DjVul/Nixie-Clock-V1/Aesthetic/DSC_0027.JPG

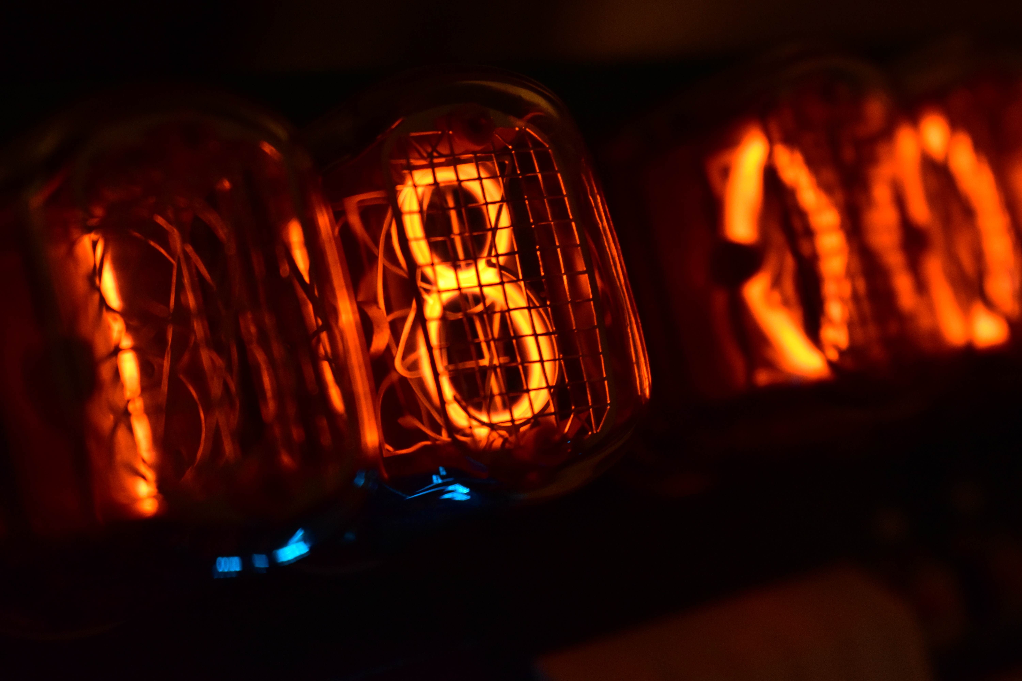
Aesthetic/DSC_0027.JPG
