DjVul/Nixie-Clock-V1/Aesthetic/DSC_0036.JPG

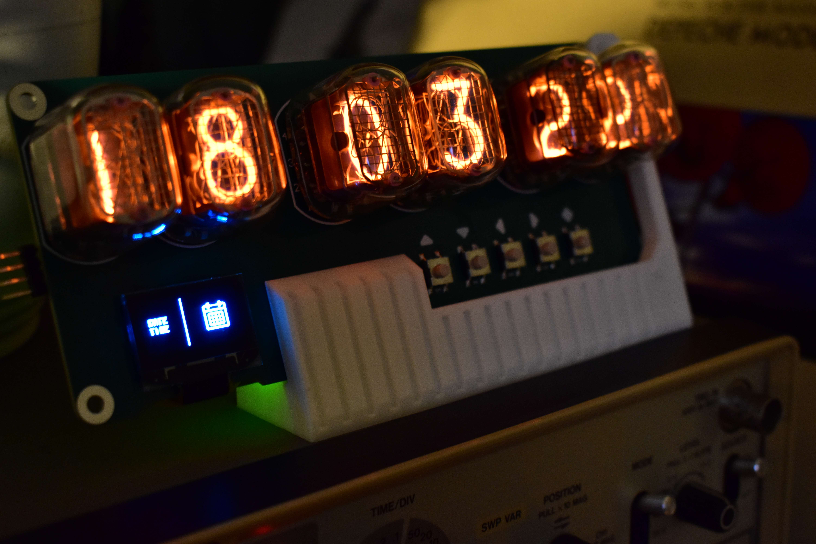
Aesthetic/DSC_0036.JPG
