DjVul/Nixie-Clock-V1/Aesthetic/DSC_0042.JPG

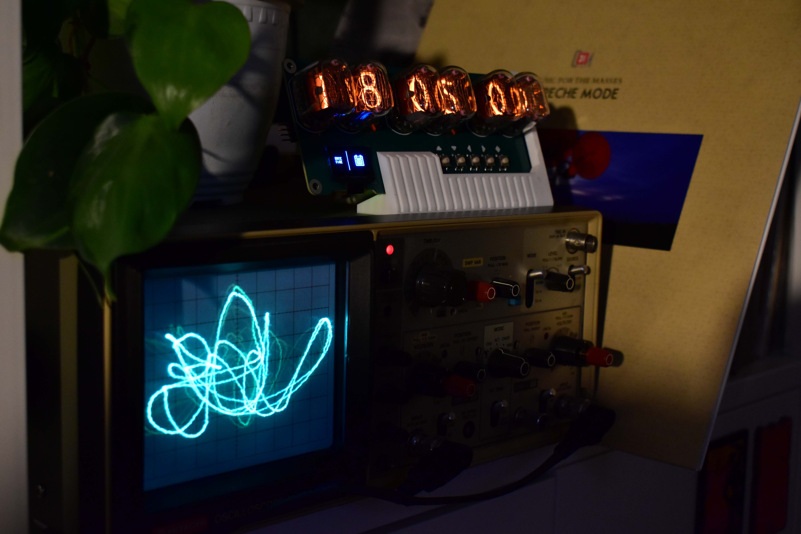
Aesthetic/DSC_0042.JPG
